Sl-Alex/GpsClock/FW/src/usr_font.c

/*
    This file is part of "GPS clock" project.

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
    Some parts of this project are written by 3-rd party vendors under a
    different license. See readme.txt for the complete list of 3-rd party
    source code.

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
    You should have received a copy of the GNU General Public License
    along with "GPS clock".  If not, see <http://www.gnu.org/licenses/>.
*/

/**
* @file usr_font.c
* @brief Simple ASCII font
* @note Code page 1251 (Cyrillic) is implemented.
* @details 6x8 raster font is implemented. The very last (sixth) column is empty,
* so is not included. It should be empty to implement small gap between symbols.
* Feel free to modify this font according to your own code page. Pay attention,
* that all localized constants in @ref usr_messages.c must be encoded in the same
* code page.
* @author Oleksii Slabchenko, alexslabchenko@gmail.com
* @copyright Oleksii Slabchenko, 2014
*/

#include "usr_font.h"

/// @brief Complete one-byte charset
const uint8_t usr_font[256][5] =
{
    {0, 0, 0, 0, 0}, // 0x00
    {0, 0, 0, 0, 0}, // 0x01
    {0, 0, 0, 0, 0}, // 0x02
    {0, 0, 0, 0, 0}, // 0x03
    {0, 0, 0, 0, 0}, // 0x04
    {0, 0, 0, 0, 0}, // 0x05
    {0, 0, 0, 0, 0}, // 0x06
    {0, 0, 0, 0, 0}, // 0x07
    {0, 0, 0, 0, 0}, // 0x08
    {0, 0, 0, 0, 0}, // 0x09
    {0, 0, 0, 0, 0}, // 0x0A
    {0, 0, 0, 0, 0}, // 0x0B
    {0, 0, 0, 0, 0}, // 0x0C
    {0, 0, 0, 0, 0}, // 0x0D
    {0, 0, 0, 0, 0}, // 0x0E
    {0, 0, 0, 0, 0}, // 0x0F
    {0, 0, 0, 0, 0}, // 0x10
    {0, 0, 0, 0, 0}, // 0x11
    {0, 0, 0, 0, 0}, // 0x12
    {0, 0, 0, 0, 0}, // 0x13
    {0, 0, 0, 0, 0}, // 0x14
    {0, 0, 0, 0, 0}, // 0x15
    {0, 0, 0, 0, 0}, // 0x16
    {0, 0, 0, 0, 0}, // 0x17
    {0, 0, 0, 0, 0}, // 0x18
    {0, 0, 0, 0, 0}, // 0x19
    {0, 0, 0, 0, 0}, // 0x1A
    {0, 0, 0, 0, 0}, // 0x1B
    {0, 0, 0, 0, 0}, // 0x1C
    {0, 0, 0, 0, 0}, // 0x1D
    {0, 0, 0, 0, 0}, // 0x1E
    {0, 0, 0, 0, 0}, // 0x1F
    {0, 0, 0, 0, 0}, // 0x20 "SPACE"
    {0b00000000,     // 0x21 "!"
     0b00000000,
     0b01001111,
     0b00000000,
     0b00000000},
    {0b00000000,     // 0x22 """
     0b00000111,
     0b00000000,
     0b00000111,
     0b00000000},
    {0b00010100,     // 0x23 "#"
     0b01111111,
     0b00010100,
     0b01111111,
     0b00010100},
    {0b00100100,     // 0x24 "$"
     0b00101010,
     0b01111111,
     0b00101010,
     0b00010010},
    {0b00100011,     // 0x25 "%"
     0b00010011,
     0b00001000,
     0b01100100,
     0b01100010},
    {0b00110110,     // 0x26 "&"
     0b01001001,
     0b01010101,
     0b00100010,
     0b01000000},
    {0b00000000,     // 0x27 "'"
     0b00000101,
     0b00000011,
     0b00000000,
     0b00000000},
    {0b00000000,     // 0x28 "("
     0b00011100,
     0b00100010,
     0b01000001,
     0b00000000},
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
    {0, 0, 0, 0, 0}, // 0x7F "DEL"
    {0, 0, 0, 0, 0}, // 0x80
    {0, 0, 0, 0, 0}, // 0x81
    {0, 0, 0, 0, 0}, // 0x82
    {0, 0, 0, 0, 0}, // 0x83
    {0, 0, 0, 0, 0}, // 0x84
    {0, 0, 0, 0, 0}, // 0x85
    {0, 0, 0, 0, 0}, // 0x86
    {0, 0, 0, 0, 0}, // 0x87
    {0b00010100,
     0b00111110,
     0b01010101,
     0b01000001,
     0b00100010}, // 0x88 "ˆ"
    {0, 0, 0, 0, 0}, // 0x89
    {0, 0, 0, 0, 0}, // 0x8A
    {0, 0, 0, 0, 0}, // 0x8B
    {0, 0, 0, 0, 0}, // 0x8C
    {0, 0, 0, 0, 0}, // 0x8D
    {0, 0, 0, 0, 0}, // 0x8E
    {0, 0, 0, 0, 0}, // 0x8F
    {0, 0, 0, 0, 0}, // 0x90
    {0, 0, 0, 0, 0}, // 0x91
    {0, 0, 0, 0, 0}, // 0x92
    {0, 0, 0, 0, 0}, // 0x93
    {0, 0, 0, 0, 0}, // 0x94
    {0, 0, 0, 0, 0}, // 0x95
    {0, 0, 0, 0, 0}, // 0x96
    {0, 0, 0, 0, 0}, // 0x97
    {0, 0, 0, 0, 0}, // 0x98
    {0, 0, 0, 0, 0}, // 0x99
    {0, 0, 0, 0, 0}, // 0x9A
    {0, 0, 0, 0, 0}, // 0x9B
    {0, 0, 0, 0, 0}, // 0x9C
    {0, 0, 0, 0, 0}, // 0x9D
    {0, 0, 0, 0, 0}, // 0x9E
    {0, 0, 0, 0, 0}, // 0x9F
    {0, 0, 0, 0, 0}, // 0xA0
    {0, 0, 0, 0, 0}, // 0xA1
    {0, 0, 0, 0, 0}, // 0xA2
    {0, 0, 0, 0, 0}, // 0xA3
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
};

// big digits  11x16 ('0..9')
// bottom to top, left to right
const uint8_t usr_digits_big[10][11*2] =
{
	{0b00111111,0b11111100,
	 0b01111111,0b11111110,
	 0b11100000,0b00000111,
	 0b11000000,0b00000011,
	 0b11000000,0b00000011,
	 0b11000000,0b00000011,
	 0b11000000,0b00000011,
	 0b11000000,0b00000011,
	 0b11100000,0b00000111,
	 0b01111111,0b11111110,
	 0b00111111,0b11111100}, // '0'
	{0b00000000,0b00000000,
	 0b00000000,0b00000000,
	 0b11000000,0b00001100,
	 0b11000000,0b00001100,
	 0b11000000,0b00001110,
	 0b11111111,0b11111111,
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
	 0b00010000,
	 0b01111100}, // '4'
	{0b01011100,
	 0b01010100,
	 0b01110100}, // '5'
	{0b01111100,
	 0b01010100,
	 0b01110000}, // '6'
	{0b00000100,
	 0b00000100,
	 0b01111100}, // '7'
	{0b01111100,
	 0b01010100,
	 0b01111100}, // '8'
	{0b01011100,
	 0b01010100,
	 0b01111100}, // '9'
};
